apshu/A8PicoCartPlus/source/Pico VSCode Project/a8_pico_cart/rom.h

unsigned char A8PicoCart_rom[] = {
  0x60, 0xad, 0x14, 0xd0, 0xc9, 0x01, 0xf0, 0x0d, 0xa9, 0x6f, 0x8d, 0xc5,
  0x02, 0xa9, 0x62, 0x8d, 0xc6, 0x02, 0x4c, 0x1f, 0xa0, 0xa9, 0x4f, 0x8d,
  0xc5, 0x02, 0xa9, 0x42, 0x8d, 0xc6, 0x02, 0xa9, 0x03, 0x85, 0x09, 0xa9,
  0xfa, 0x85, 0x02, 0xa9, 0xa3, 0x85, 0x03, 0x20, 0x1c, 0xa6, 0x20, 0xea,
  0xa7, 0x20, 0x01, 0xa8, 0x20, 0x59, 0xa5, 0x20, 0x9d, 0xa2, 0xad, 0x10,
  0xd0, 0xd0, 0x03, 0x20, 0x5b, 0xa4, 0xa9, 0x06, 0x20, 0x20, 0x06, 0xad,
  0x01, 0xd5, 0xf0, 0x13, 0xc9, 0x02, 0xb0, 0x0c, 0xa9, 0x01, 0x85, 0x80,
  0xad, 0x02, 0xd5, 0x85, 0x85, 0x4c, 0x01, 0xa2, 0x20, 0x04, 0xa4, 0xa9,
  0x00, 0x85, 0x87, 0xa9, 0x01, 0x20, 0x20, 0x06, 0xad, 0x01, 0xd5, 0xc9,
  0x01, 0xd0, 0x06, 0x20, 0x04, 0xa4, 0x4c, 0x5f, 0xa0, 0xad, 0x02, 0xd5,
  0x85, 0x80, 0xa9, 0x00, 0x85, 0x84, 0xa9, 0x00, 0x85, 0x85, 0x20, 0x8b,
  0xa6, 0x20, 0x04, 0xa5, 0xa5, 0x80, 0xd0, 0x09, 0x20, 0xb6, 0xa6, 0x20,
  0xd2, 0xa5, 0x4c, 0x9b, 0xa0, 0x20, 0xa7, 0xa4, 0x20, 0x39, 0xa5, 0x20,
  0xe8, 0xa2, 0x20, 0x47, 0xa5, 0xf0, 0x71, 0xc9, 0x2b, 0xd0, 0x03, 0x4c,
  0x37, 0xa2, 0xc9, 0x1b, 0xd0, 0x03, 0x4c, 0x37, 0xa2, 0xc9, 0x1e, 0xd0,
  0x03, 0x4c, 0x37, 0xa2, 0xc9, 0x9b, 0xd0, 0x03, 0x4c, 0x01, 0xa2, 0xc9,
  0x62, 0xd0, 0x03, 0x4c, 0x45, 0xa2, 0xc9, 0x66, 0xd0, 0x03, 0x4c, 0x69,
  0xa2, 0xc9, 0x2f, 0xd0, 0x03, 0x4c, 0x69, 0xa2, 0xc9, 0x3e, 0xd0, 0x03,
  0x4c, 0x6e, 0xa1, 0xc9, 0x8f, 0xd0, 0x03, 0x4c, 0x6e, 0xa1, 0xc9, 0x3c,
  0xd0, 0x03, 0x4c, 0xd1, 0xa1, 0xc9, 0x8e, 0xd0, 0x03, 0x4c, 0xd1, 0xa1,
  0xc9, 0x90, 0xd0, 0x03, 0x4c, 0xee, 0xa1, 0xc9, 0x91, 0xd0, 0x03, 0x4c,
  0x96, 0xa1, 0xc9, 0x1c, 0xd0, 0x03, 0x4c, 0xba, 0xa1, 0xc9, 0x2d, 0xd0,
  0x03, 0x4c, 0xba, 0xa1, 0xc9, 0x1d, 0xf0, 0x40, 0xc9, 0x3d, 0xf0, 0x3c,
  0x20, 0xaf, 0xa2, 0xa5, 0x8b, 0xc9, 0x01, 0xd0, 0x03, 0x4c, 0x01, 0xa2,
  0xa5, 0x8c, 0x29, 0x01, 0xf0, 0x03, 0x4c, 0xba, 0xa1, 0xa5, 0x8c, 0x29,
  0x02, 0xf0, 0x03, 0x4c, 0x50, 0xa1, 0xa5, 0x8c, 0x29, 0x04, 0xf0, 0x03,
  0x4c, 0x37, 0xa2, 0xad, 0x70, 0x02, 0xcd, 0x00, 0x01, 0xf0, 0x0a, 0x8d,
  0x00, 0x01, 0x49, 0xe4, 0xd0, 0x03, 0x4c, 0x37, 0xa2, 0x4c, 0x9b, 0xa0,
  0xa5, 0x85, 0x18, 0x69, 0x01, 0xc5, 0x80, 0x90, 0x03, 0x4c, 0x9b, 0xa0,
  0xe6, 0x85, 0xa5, 0x85, 0x38, 0xe5, 0x84, 0x18, 0xc9, 0x0f, 0xf0, 0x48,
  0x20, 0x39, 0xa5, 0x4c, 0x9b, 0xa0, 0xa5, 0x85, 0x18, 0x69, 0x0f, 0x90,
  0x03, 0x4c, 0x81, 0xa1, 0xc5, 0x80, 0xb0, 0x05, 0x85, 0x85, 0x4c, 0xb0,
  0xa1, 0xa5, 0x80, 0x38, 0xe9, 0x01, 0x85, 0x85, 0x38, 0xe5, 0x84, 0x18,
  0xc9, 0x0f, 0xb0, 0x20, 0x20, 0x39, 0xa5, 0x4c, 0x9b, 0xa0, 0xa5, 0x80,
  0x38, 0xe9, 0x01, 0x85, 0x85, 0xa5, 0x84, 0x18, 0x69, 0x0f, 0xb0, 0x04,
  0xc5, 0x80, 0x90, 0xf7, 0x38, 0xe9, 0x0f, 0x85, 0x84, 0x4c, 0x82, 0xa0,
  0xa5, 0x84, 0x18, 0x69, 0x0f, 0x85, 0x84, 0x4c, 0x82, 0xa0, 0xa5, 0x85,
  0xc9, 0x00, 0xd0, 0x03, 0x4c, 0x9b, 0xa0, 0xc6, 0x85, 0xa5, 0x85, 0xc5,
  0x84, 0x30, 0x2c, 0x20, 0x39, 0xa5, 0x4c, 0x9b, 0xa0, 0xa5, 0x85, 0x38,
  0xe9, 0x0f, 0x90, 0x05, 0x85, 0x85, 0x4c, 0xf7, 0xa1, 0xa5, 0x85, 0xd0,
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
};
unsigned int A8PicoCart_rom_len = 8192;
